Schievel1/dactyl_manuform_r_track/images/layer0.jpg

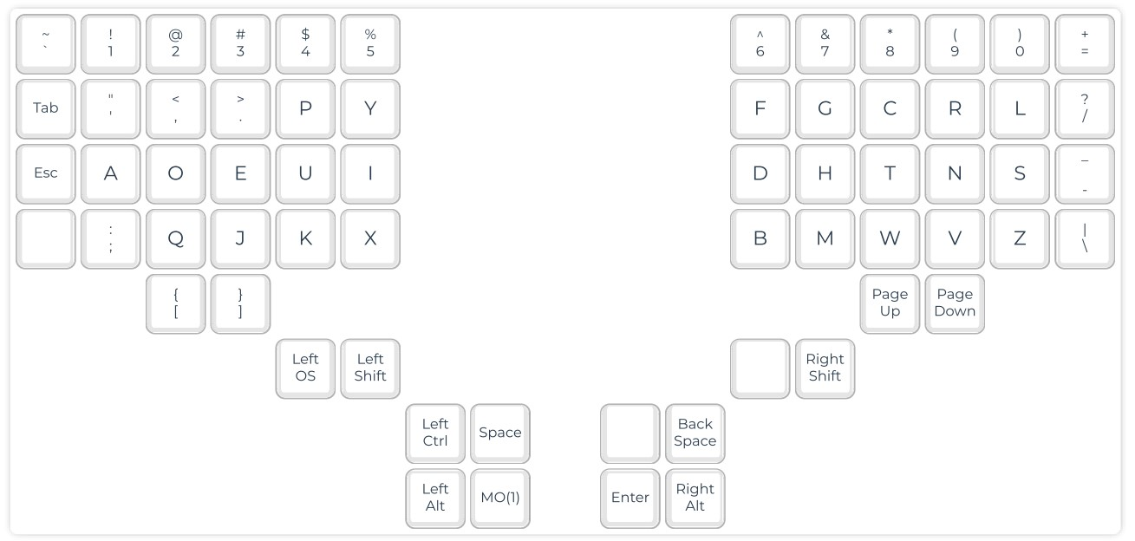
images/layer0.jpg
