Schievel1/dactyl_manuform_r_track/images/layer1.jpg

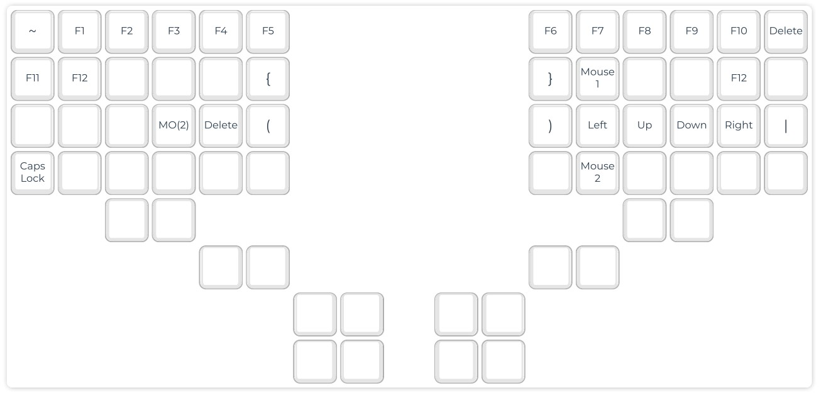
images/layer1.jpg
