Schievel1/dactyl_manuform_r_track/images/more_images/IMG_9903.jpg

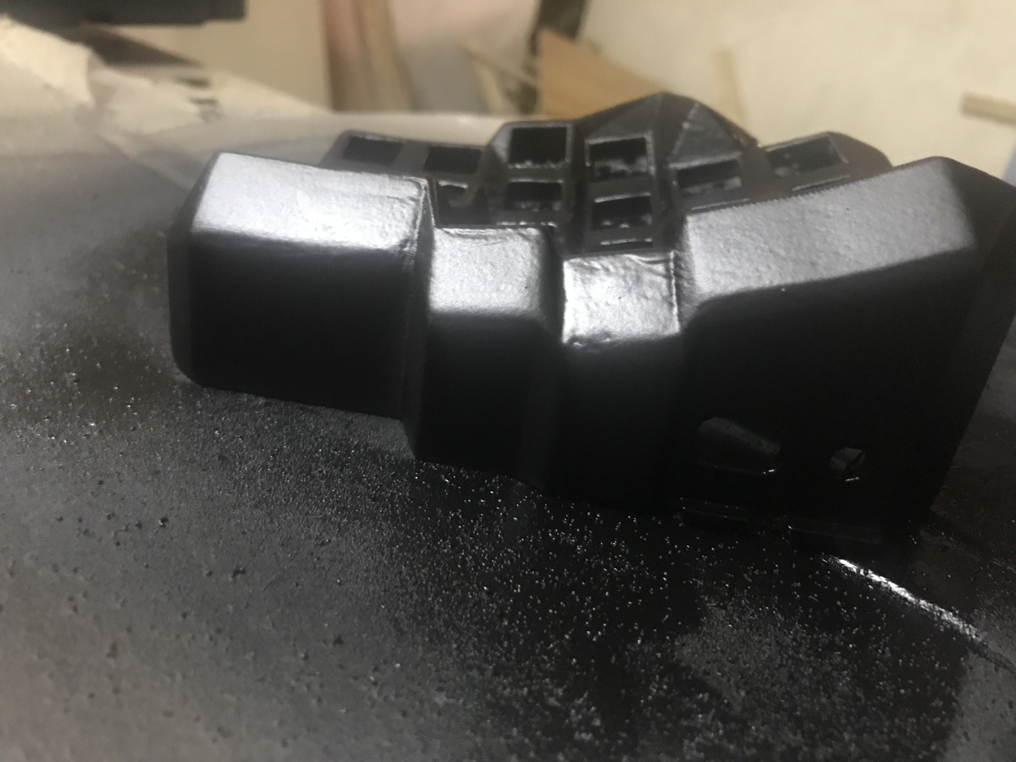
images/more_images/IMG_9903.jpg
