Schievel1/dactyl_manuform_r_track/images/more_images/IMG_9917.jpg

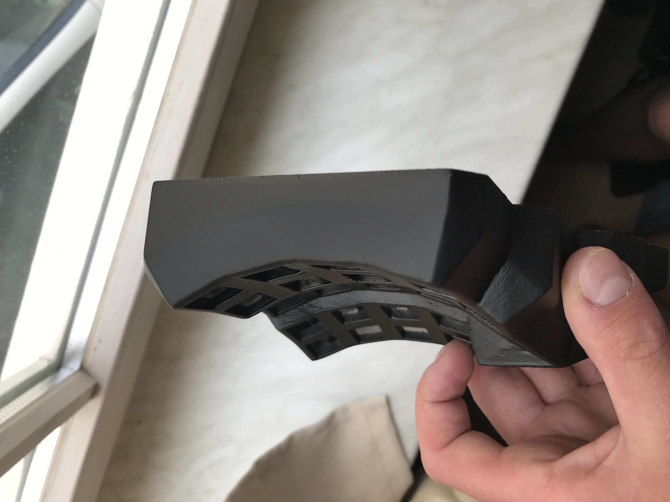
images/more_images/IMG_9917.jpg
