Schievel1/dactyl_manuform_r_track/images/more_images/IMG_9927.jpg

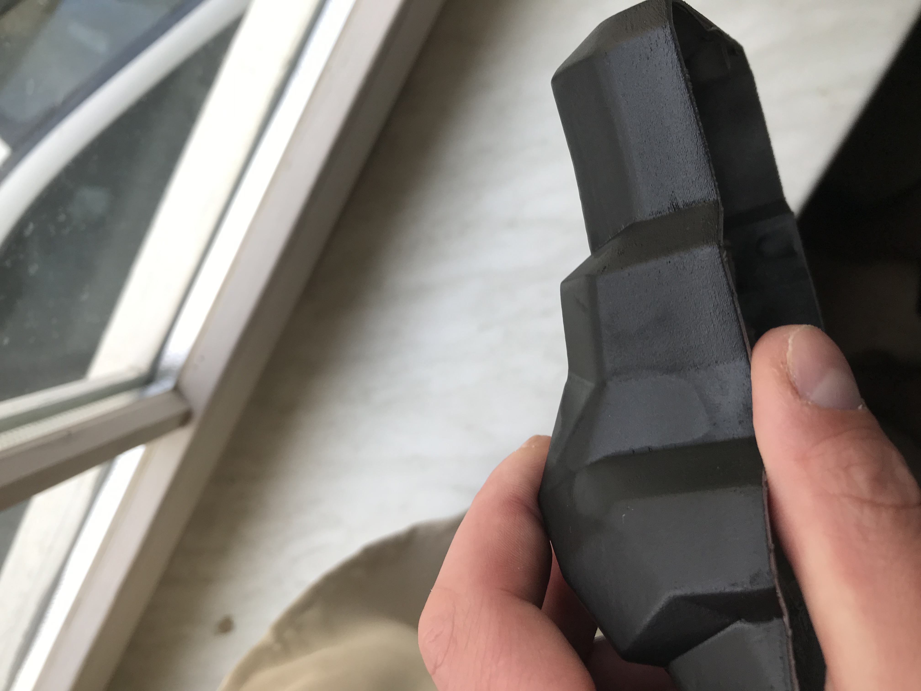
images/more_images/IMG_9927.jpg
