Schievel1/dactyl_manuform_r_track/images/more_images/IMG_9942.jpg

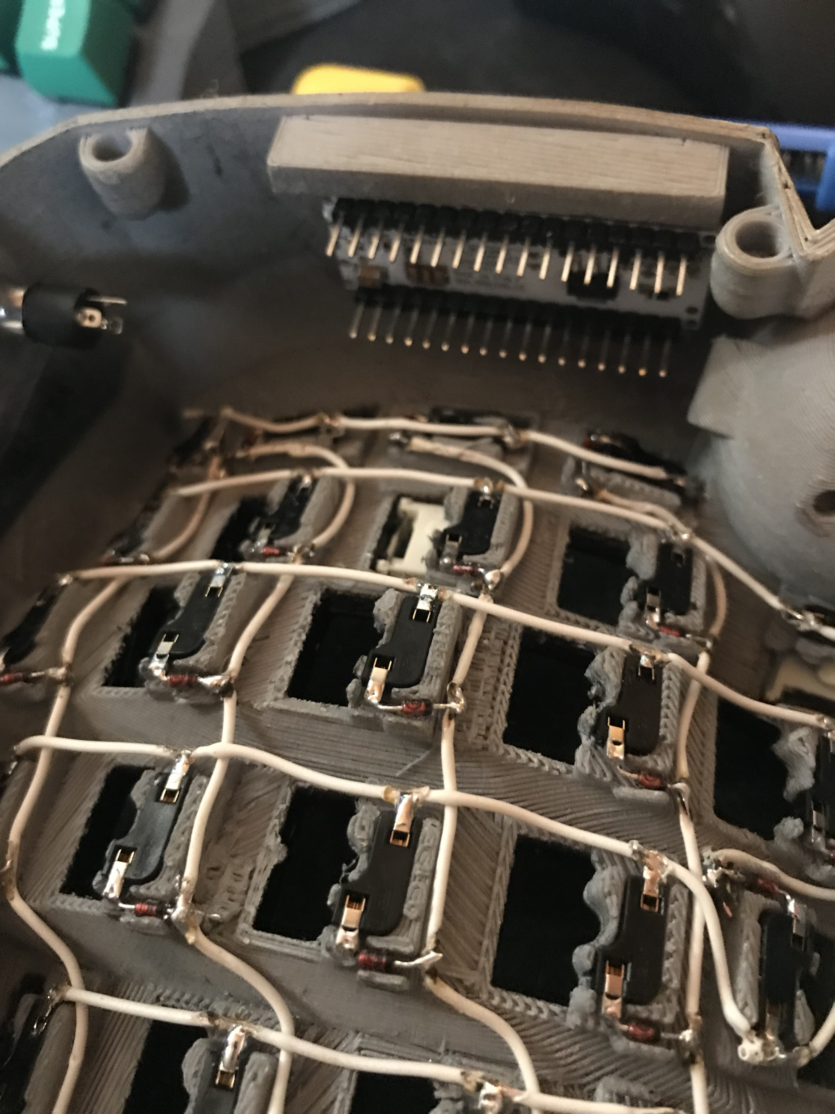
images/more_images/IMG_9942.jpg
