Schievel1/dactyl_manuform_r_track/images/wokk.jpg

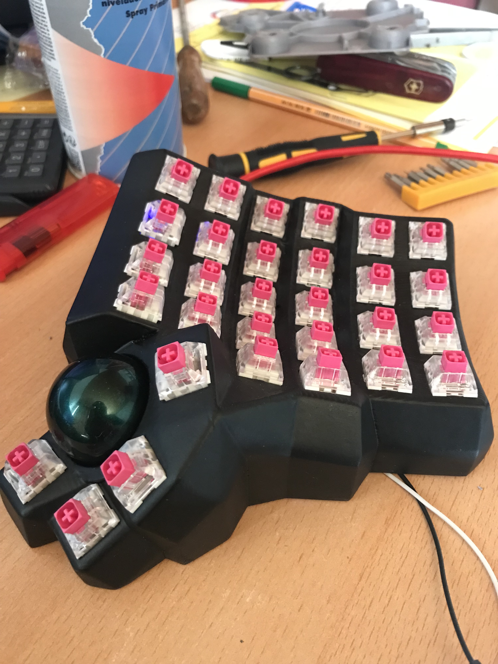
images/wokk.jpg
